Solartraveler/irusb/src-device/Inc/main.h

#define IrRxPower_Pin GPIO_PIN_4
#define IrRxPower_GPIO_Port GPIOA
#define IrRxIn_Pin GPIO_PIN_6
#define IrRxIn_GPIO_Port GPIOA
#define LedRed_Pin GPIO_PIN_15
#define LedRed_GPIO_Port GPIOA
#define UsbReset_Pin GPIO_PIN_3
#define UsbReset_GPIO_Port GPIOB
